WiddleWabbit/MQTT-Module-Sensor/Outputs/Models/MQTT-Module-CurrentSensors-Back.png

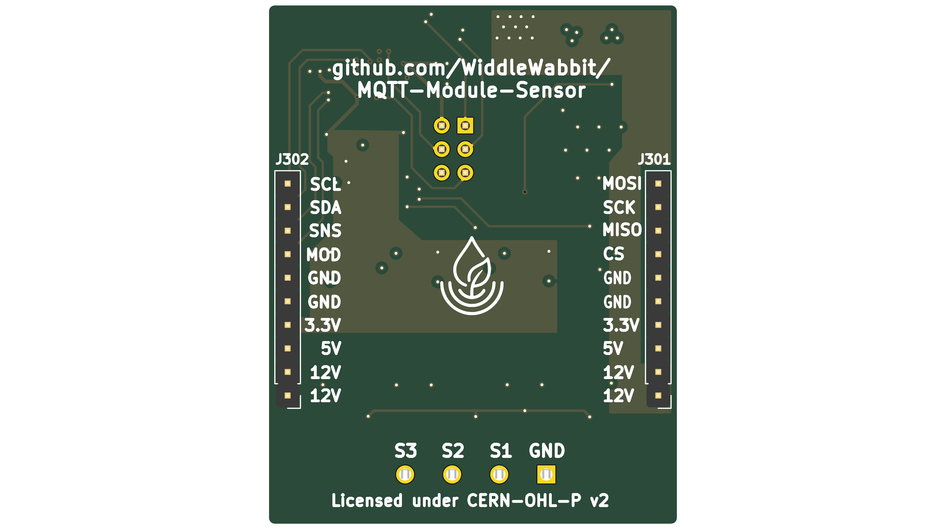
Outputs/Models/MQTT-Module-CurrentSensors-Back.png
