WiddleWabbit/MQTT-Module-Sensor/Outputs/Models/MQTT-Module-CurrentSensors-Front.png

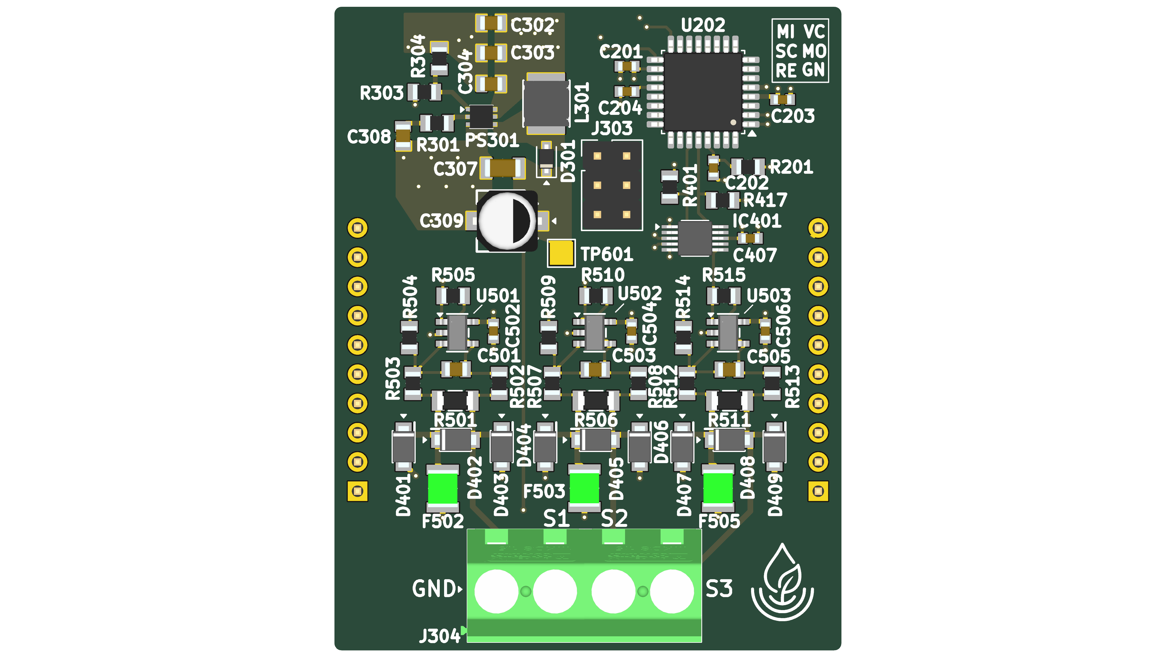
Outputs/Models/MQTT-Module-CurrentSensors-Front.png
